maslohaslo1234-spec/snek-8x8/hardware/snek_pcb_kicad.kicad_sch

## KiCad design hardware/snek_pcb_kicad.kicad_sch (2026-10-03)

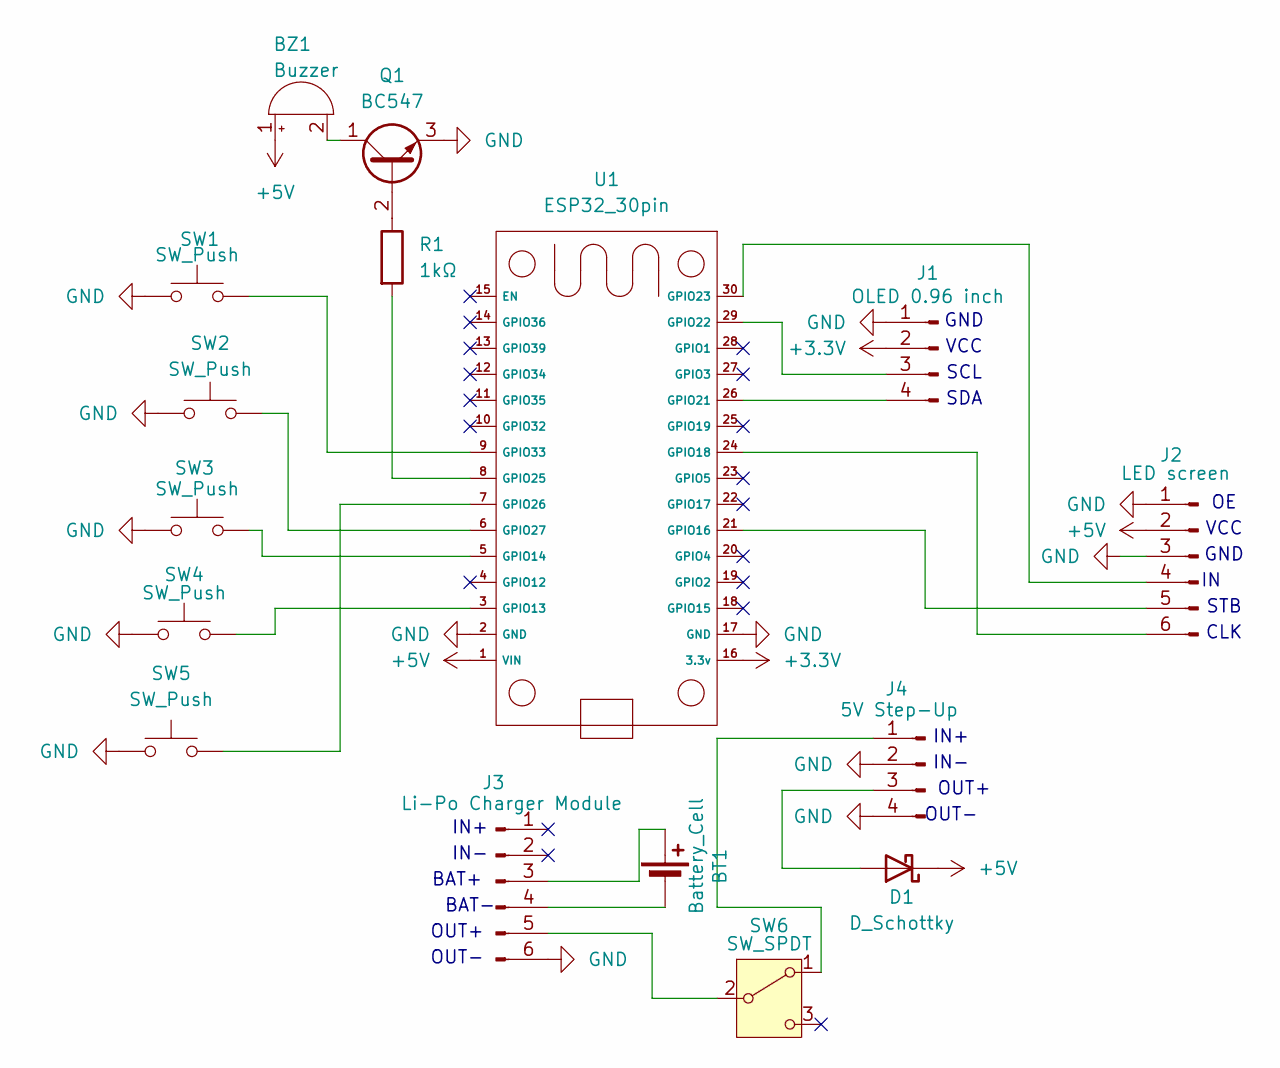
[picture p2: schematic snek_pcb_kicad.kicad_sch]

Parts:
BT1: Battery_Cell; Texas_DRC0010J_ThermalVias
BZ1: Buzzer; Texas_RVA_VQFN-16-1EP_3.5x3.5mm_P0.5mm_EP2.14x2.14mm_Therma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
D1: D_Schottky
J1: OLED 0.96 inch; ESP32_30pin
J2: LED screen
J3: Li-Po Charger Module
J4: 5V Step-Up; ESP32_30pin
Q1: BC547; TO-92_Inline
R1: 1kΩ
SW1, SW5: SW_Push; SW_NKK_GW12LJP
SW2, SW3, SW4: SW_Push
SW6: SW_SPDT
U1: ESP32_30pin

Connections:
+3.3V: J1.2, U1.16 (3.3v)
+5V: BZ1.1 (+), D1.1 (K), J2.2, U1.1 (VIN)
GND: J1.1, J2.1, J2.3, J3.6, J4.2, J4.4, Q1.3 (E), SW1.1, SW2.1, SW3.1, SW4.1, SW5.1, U1.2 (GND), U1.17 (GND)
unnamed: BT1.1 (+), J3.3
unnamed: BT1.2 (-), J3.4
unnamed: BZ1.2 (-), Q1.1 (C)
unnamed: D1.2 (A), J4.3
unnamed: J1.3, U1.29 (GPIO22)
unnamed: J1.4, U1.26 (GPIO21)
unnamed: J2.4, U1.30 (GPIO23)
unnamed: J2.5, U1.21 (GPIO16)
unnamed: J2.6, U1.24 (GPIO18)
unnamed: J3.5, SW6.2 (B)
unnamed: J4.1, SW6.1 (A)
unnamed: Q1.2 (B), R1.1
unnamed: R1.2, U1.8 (GPIO25)
unnamed: SW1.2, U1.9 (GPIO33)
unnamed: SW2.2, U1.6 (GPIO27)
unnamed: SW3.2, U1.5 (GPIO14)
unnamed: SW4.2, U1.3 (GPIO13)
unnamed: SW5.2, U1.7 (GPIO26)

Notes on the sheet:
IN+
OUT-
GND
STB
OUT+
VCC
CLK
SDA
IN-
BAT-
BAT+
SCL
